windnerd-labs/Anemometer-3D-files/sunbank-2w/3-mast-dock-20mm.stl

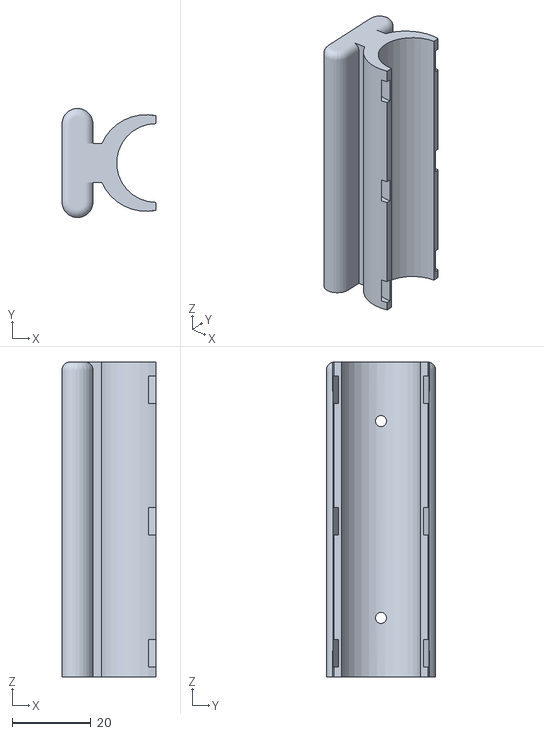
[picture p24: CAD file, 2026-02-20]
sunbank-2w/3-mast-dock-20mm.stl
23.9 x 27.7 x 80.0
