windnerd-labs/Anemometer-3D-files/anemometer-head/3-support-up.stl

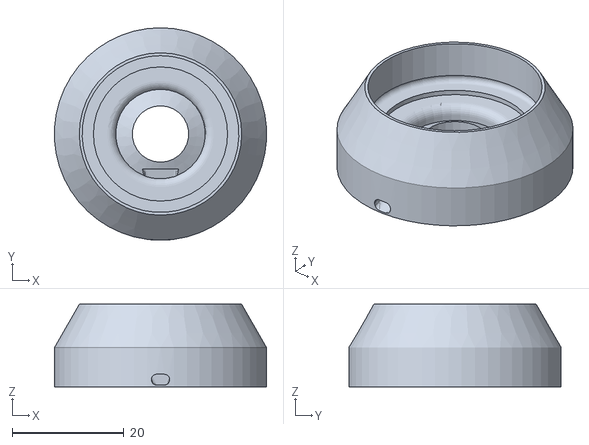
[picture p25: CAD file, 2026-10-04]
anemometer-head/3-support-up.stl
37.9 x 38.0 x 14.8
