windnerd-labs/Anemometer-3D-files/receptacles/sunbank-2w/2-bottom-cover.stl

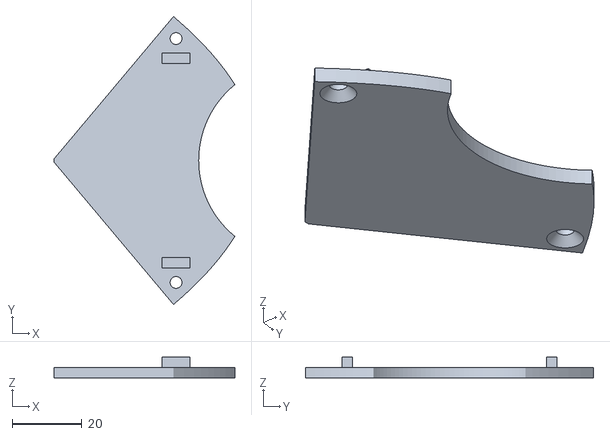
[picture p26: CAD file, 2026-02-19]
receptacles/sunbank-2w/2-bottom-cover.stl
51.9 x 82.7 x 6.00
