windnerd-labs/Anemometer-3D-files/receptacles/top-mast-mount/1-top-mast-mount-42mm.stl

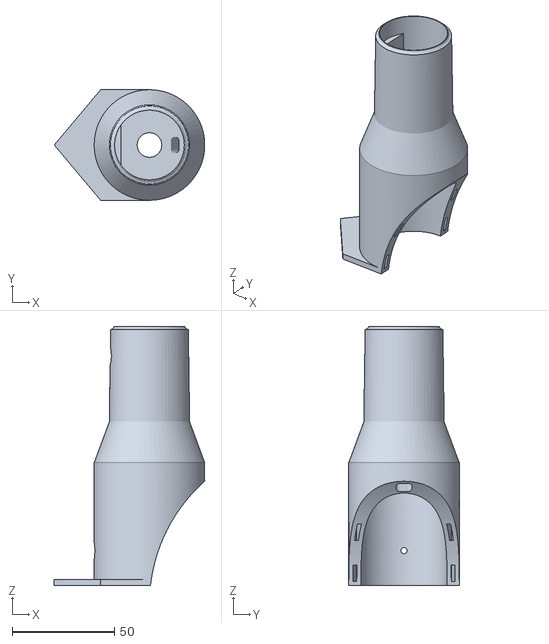
[picture p27: CAD file, 2025-11-19]
receptacles/top-mast-mount/1-top-mast-mount-42mm.stl
73.5 x 54.0 x 126.5
