windnerd-labs/Anemometer-3D-files/sunbank-2w/3-mast-dock-32mm.stl

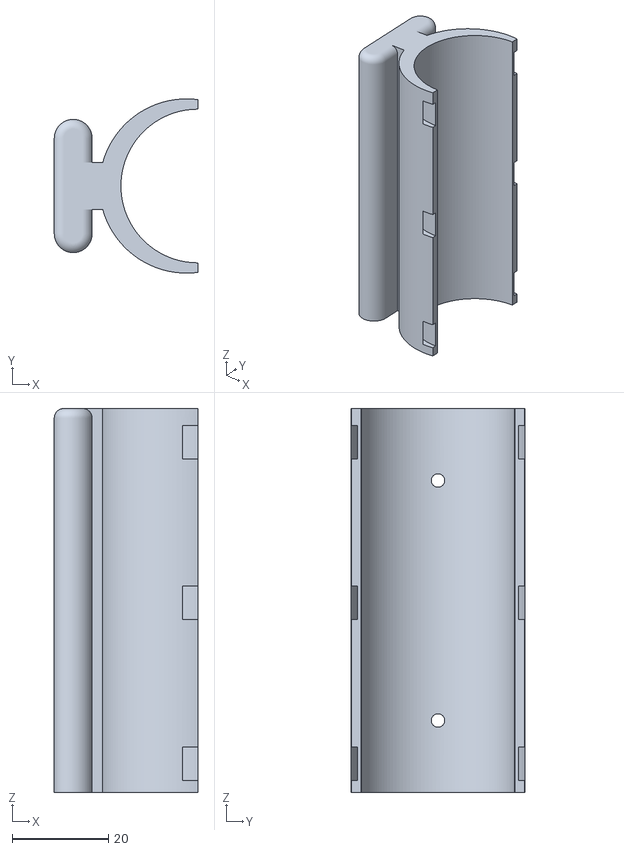
[picture p28: CAD file, 2026-02-20]
sunbank-2w/3-mast-dock-32mm.stl
29.9 x 36.3 x 80.0
