windnerd-labs/Anemometer-3D-files/anemometer-head/6-cups-axle.stl

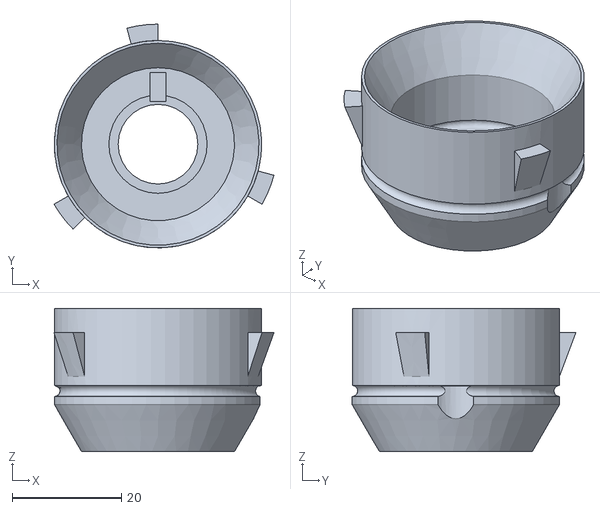
[picture p29: CAD file, 2026-10-04]
anemometer-head/6-cups-axle.stl
40.3 x 41.0 x 26.3
