windnerd-labs/Anemometer-3D-files/receptacles/top-mast-mount/1-top-mast-mount-20mm.stl

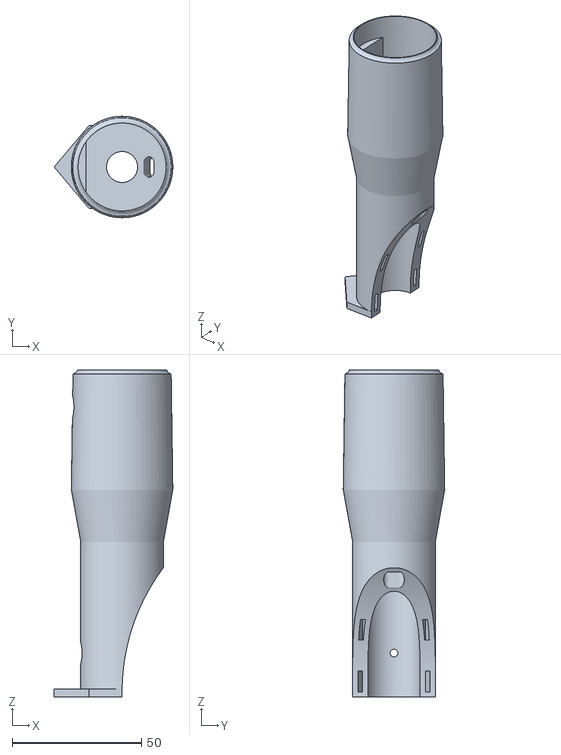
[picture p30: CAD file, 2025-11-19]
receptacles/top-mast-mount/1-top-mast-mount-20mm.stl
45.9 x 39.3 x 126.5
