windnerd-labs/Anemometer-3D-files/sunbank-2w/3-mast-dock-42mm.stl

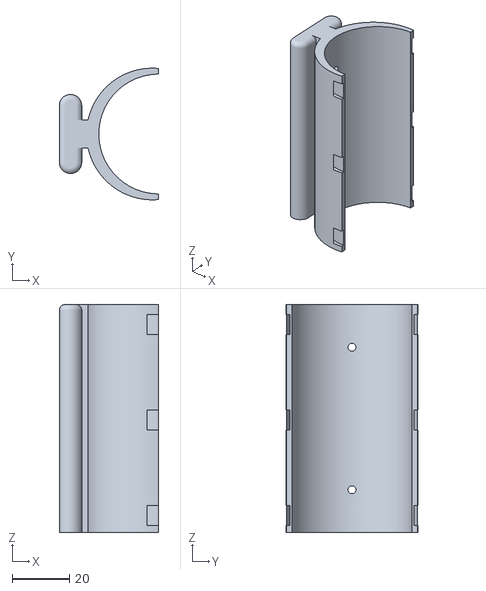
[picture p31: CAD file, 2026-02-20]
sunbank-2w/3-mast-dock-42mm.stl
34.9 x 46.2 x 80.0
