windnerd-labs/Anemometer-3D-files/anemometer-head/7-pcb-housing.stl

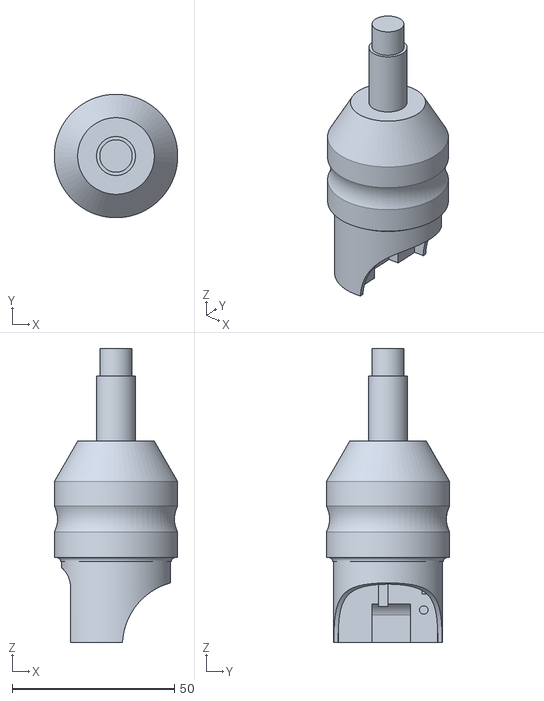
[picture p32: CAD file, 2026-10-04]
anemometer-head/7-pcb-housing.stl
38.0 x 38.0 x 90.5
