windnerd-labs/Anemometer-3D-files/receptacles/top-mast-mount/1-top-mast-mount-40mm.stl

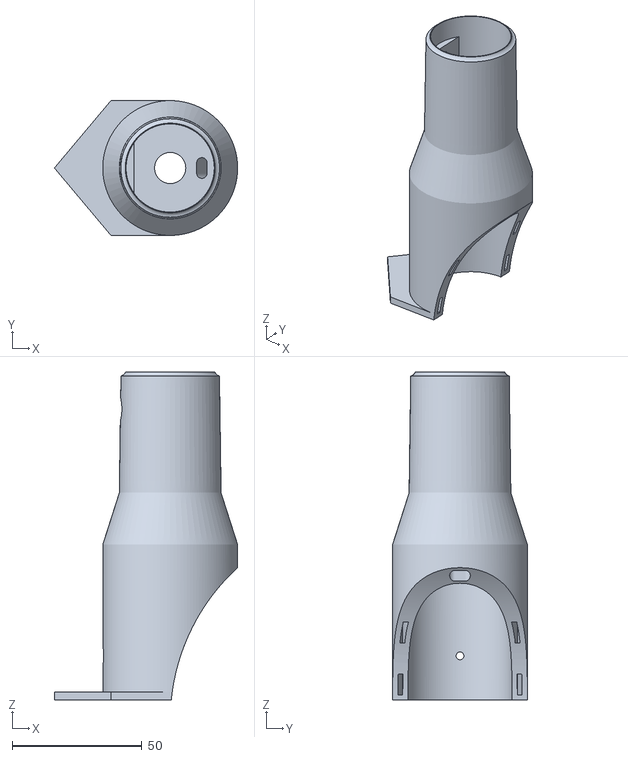
[picture p33: CAD file, 2025-11-19]
receptacles/top-mast-mount/1-top-mast-mount-40mm.stl
70.7 x 52.0 x 126.5
