windnerd-labs/Anemometer-3D-files/sunbank-2w/3-mast-dock-40mm.stl

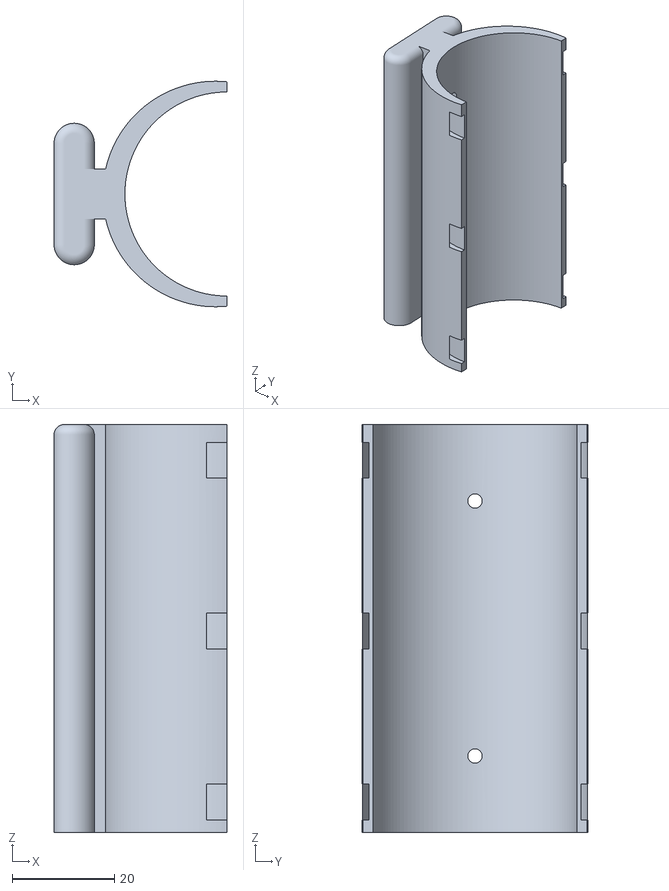
[picture p34: CAD file, 2026-02-20]
sunbank-2w/3-mast-dock-40mm.stl
33.9 x 44.2 x 80.0
