windnerd-labs/Anemometer-3D-files/anemometer-head/1-vane-south-hemisphere.stl

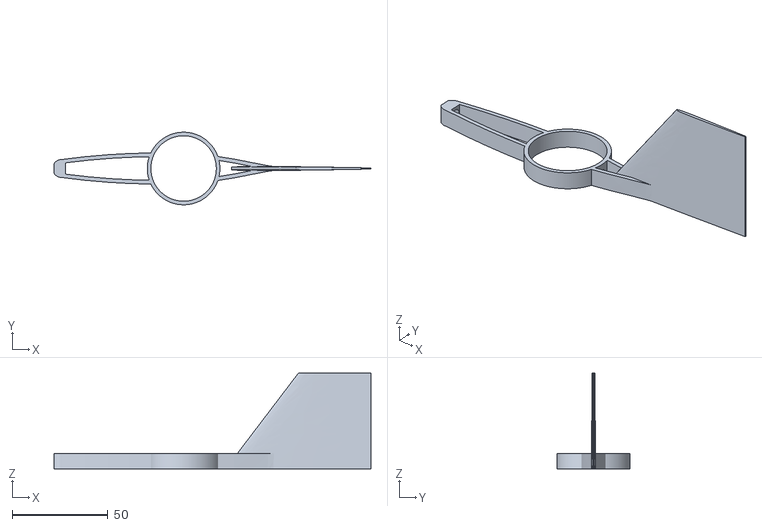
[picture p35: CAD file, 2026-07-27]
anemometer-head/1-vane-south-hemisphere.stl
165.8 x 38.0 x 50.0
