windnerd-labs/Anemometer-3D-files/sunbank-2w/3-mast-dock-30mm.stl

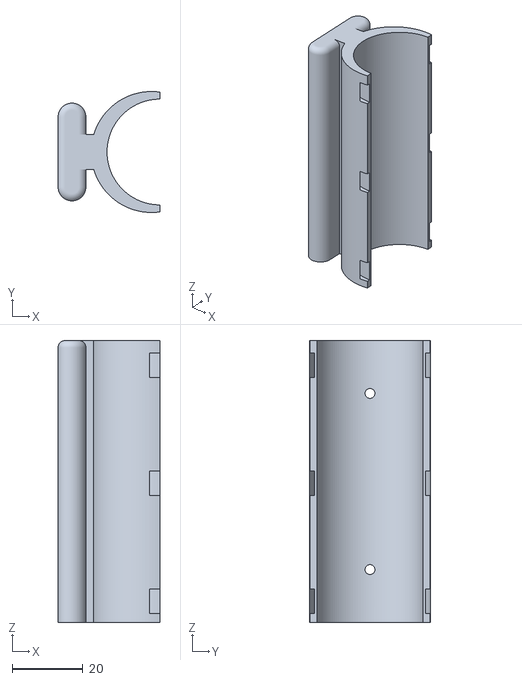
[picture p36: CAD file, 2026-02-20]
sunbank-2w/3-mast-dock-30mm.stl
28.9 x 34.3 x 80.0
