windnerd-labs/Anemometer-3D-files/receptacles/top-mast-mount/1-top-mast-mount-32mm.stl

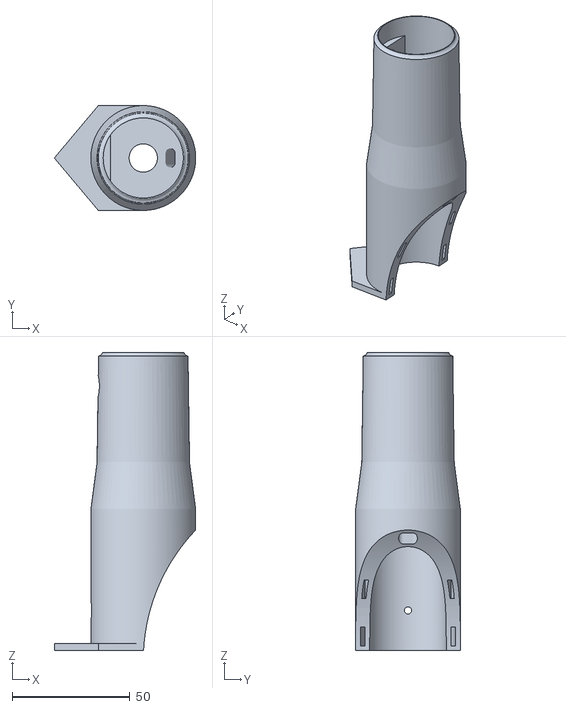
[picture p37: CAD file, 2025-11-19]
receptacles/top-mast-mount/1-top-mast-mount-32mm.stl
60.0 x 44.5 x 126.5
