windnerd-labs/Anemometer-3D-files/sunbank-2w/3-mast-dock-52mm.stl

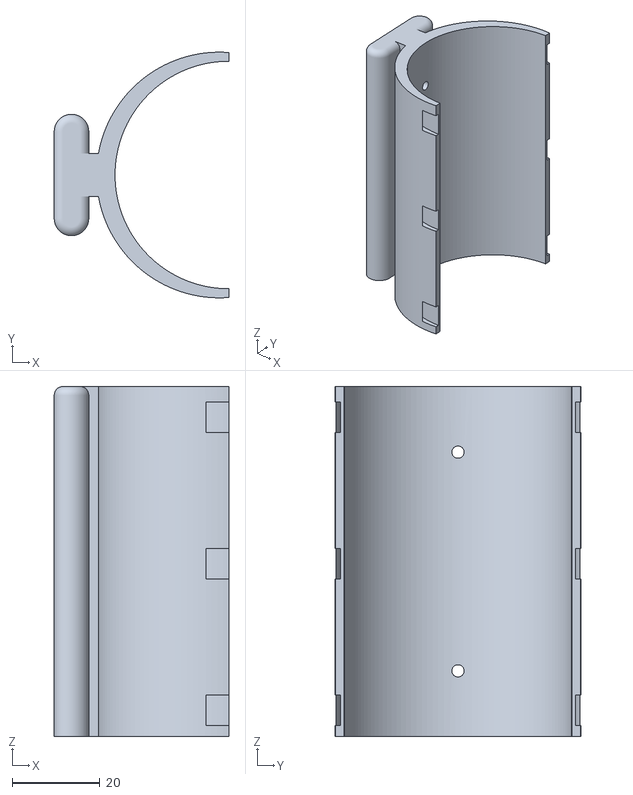
[picture p38: CAD file, 2026-02-20]
sunbank-2w/3-mast-dock-52mm.stl
39.9 x 56.2 x 80.0
