windnerd-labs/Anemometer-3D-files/anemometer-head/5-cups.stl

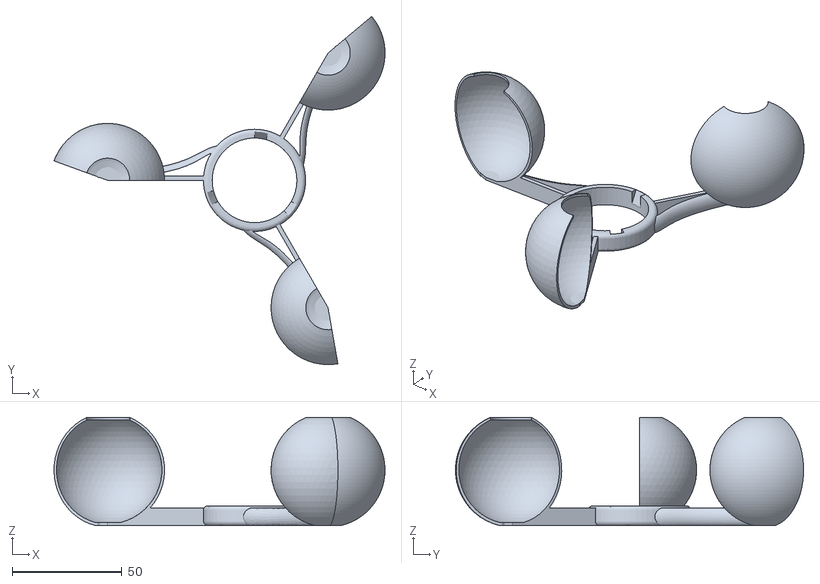
[picture p39: CAD file, 2026-07-26]
anemometer-head/5-cups.stl
150.9 x 158.7 x 49.3
