windnerd-labs/Anemometer-3D-files/receptacles/top-mast-mount/1-top-mast-mount-10mm.stl

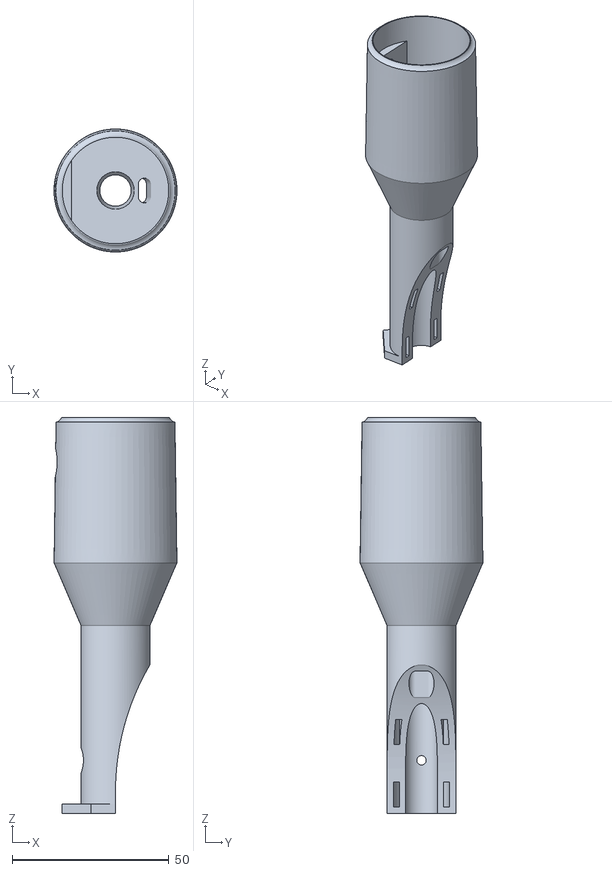
[picture p40: CAD file, 2025-11-19]
receptacles/top-mast-mount/1-top-mast-mount-10mm.stl
39.3 x 39.3 x 126.5
