windnerd-labs/Anemometer-3D-files/sunbank-2w/3-mast-dock-48mm.stl

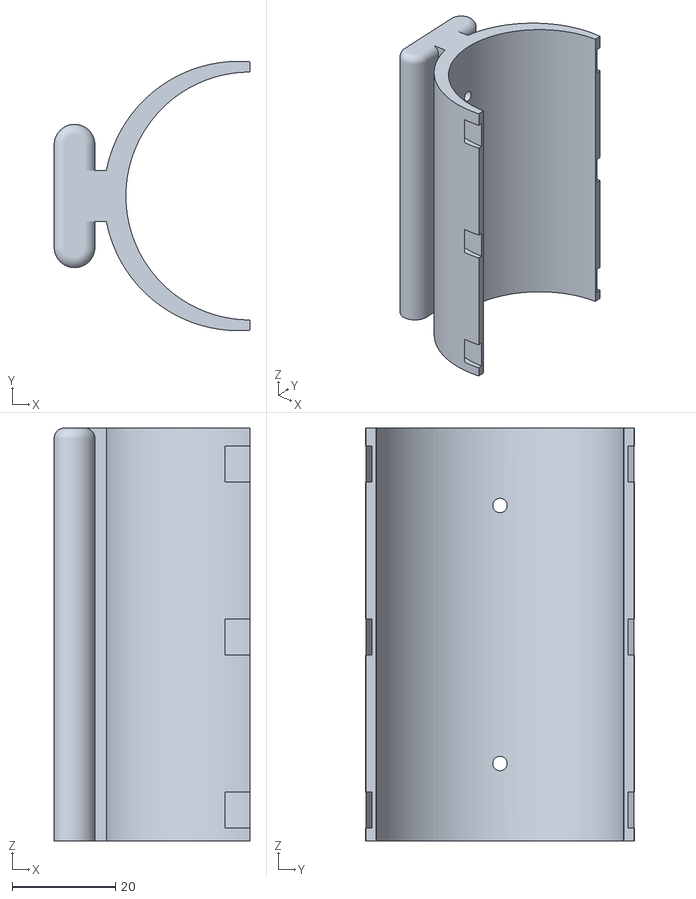
[picture p41: CAD file, 2026-02-20]
sunbank-2w/3-mast-dock-48mm.stl
37.9 x 52.2 x 80.0
